apdlv72/Frotect/android/screenshots/01_main_unconnected.png

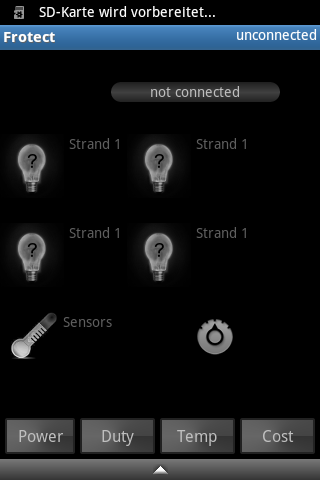
android/screenshots/01_main_unconnected.png
