apdlv72/Frotect/android/screenshots/02_opions_menu.png

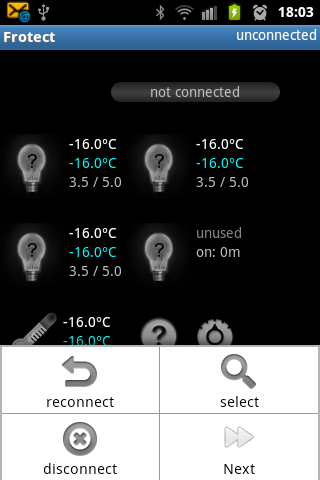
android/screenshots/02_opions_menu.png
