apdlv72/Frotect/android/screenshots/04_dialog_strand.png

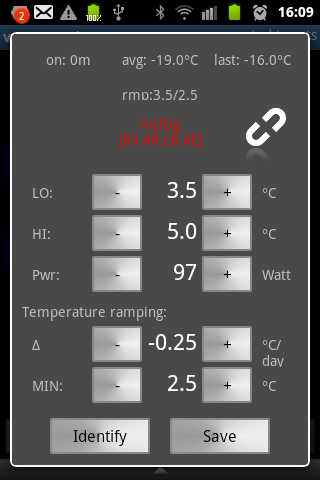
android/screenshots/04_dialog_strand.png
