apdlv72/Frotect/android/screenshots/05_dialog_sensors.png

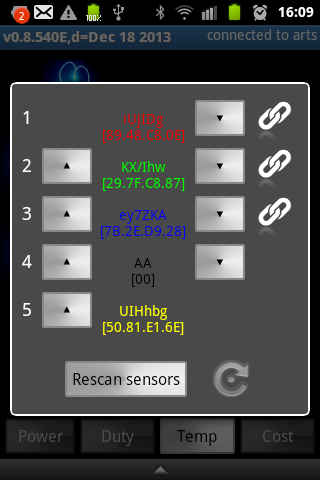
android/screenshots/05_dialog_sensors.png
