apdlv72/Frotect/android/screenshots/06_dialog_settings.png

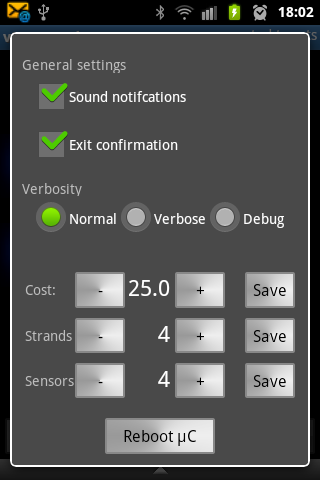
android/screenshots/06_dialog_settings.png
