apdlv72/Frotect/android/screenshots/08_stats_temperature.png

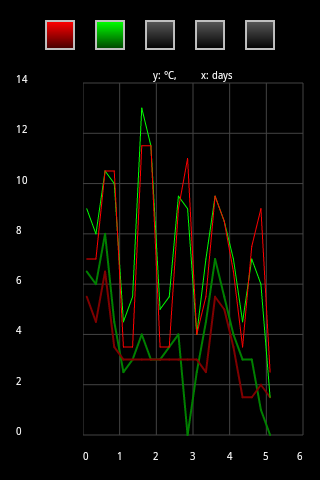
android/screenshots/08_stats_temperature.png
