apdlv72/Frotect/android/screenshots/09_stats_dutycycle.png

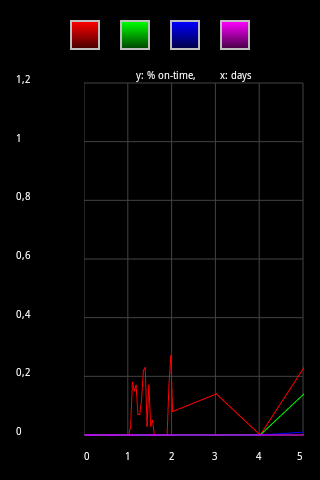
android/screenshots/09_stats_dutycycle.png
