apdlv72/Frotect/android/screenshots/10_stats_power.png

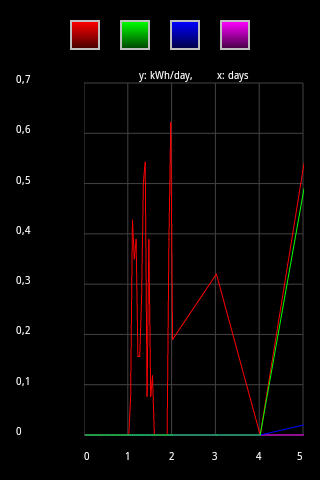
android/screenshots/10_stats_power.png
