apdlv72/Frotect/android/screenshots/11_stats_cost.png

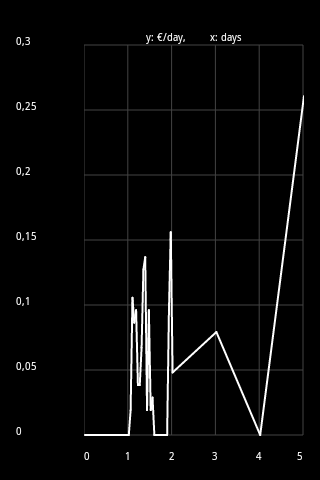
android/screenshots/11_stats_cost.png
